wyolum/LotR_Lamp/fabricate/data/Arduino_Nano_Pinout.png

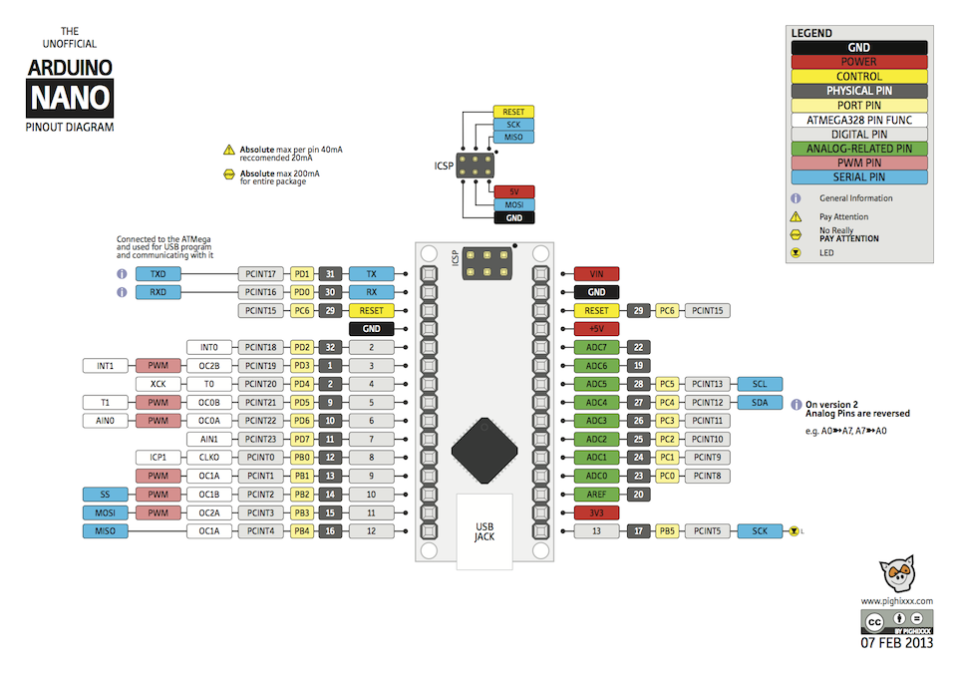
fabricate/data/Arduino_Nano_Pinout.png
