wyolum/LotR_Lamp/fabricate/gcode/LotR_Base4-Base.3mf

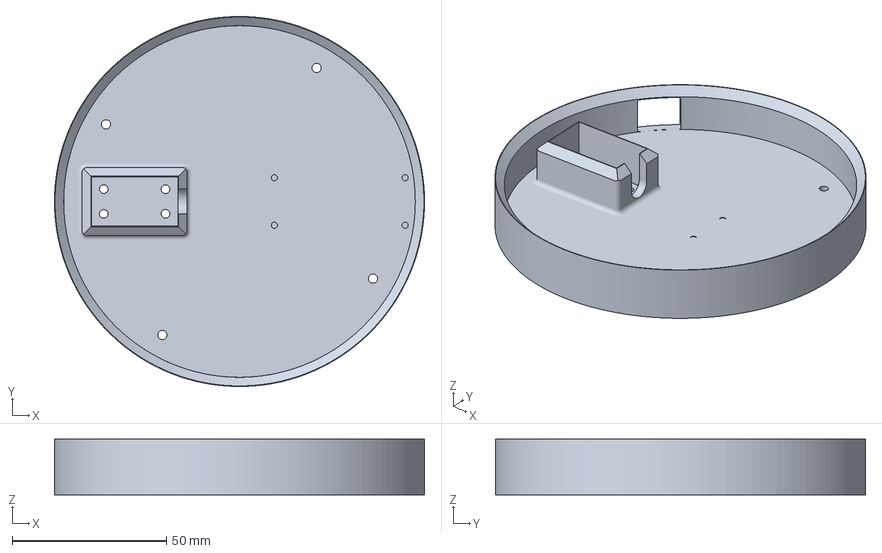
[picture p26: CAD file, 2024-11-22]
fabricate/gcode/LotR_Base4-Base.3mf
120.0 x 120.0 x 18.0 mm
