wyolum/LotR_Lamp/fabricate/data/nano-dimensions.png

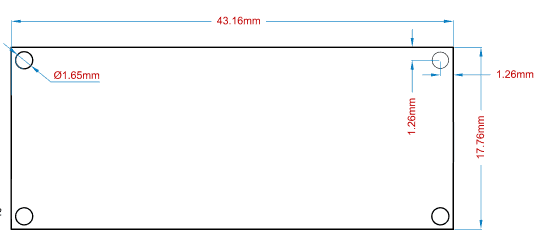
fabricate/data/nano-dimensions.png
